laforestlabs/LLUPS/ROADMAP.md

# LLUPS Roadmap

> **Last updated:** 2026-05-04
> **Current phase:** Phase 7 -- parent composition quality tuning (board shrink + SMT-over-THT stacking)
> **Quick status:** Cluster-slide post-pass (KiCraft `072ceb6`) drops parent area 18-29% on seeds 4/7/42 by pulling drifting edge/corner-pinned components back into the cluster bbox after `solve()`. Best result: seed 7 at 11,058 mm² (was 15,400+). Follow-up `bbox_packing` sub-metric (KiCraft `a1456db`) adds an in-SA signal that drift costs PCB area, but at its current weight (0.01) it's below the SA temperature noise floor — plumbing is correct, layout impact is below detection threshold. KiCraft tests: 493 pass.

---

## How to use this file

This is the **single canonical plan document** for the LLUPS project. Every session should:
1. **Start** by reading this file to understand current state
2. **End** by updating the checkboxes, status line, and Last Session section below

This is the canonical plan; the CHANGELOG remains for detailed per-session engineering notes (append-only history).

---

## Phases Overview

| # | Phase | Status | Description |
|---|---|---|---|
| 0 | Repo cleanup and KiCraft extraction | Done | Untrack artifacts, consolidate docs, extract KiCraft submodule |
| 1 | KiCraft dead code removal (Wave 1-3) | Done | Delete dead code, fix imports, clean GUI |
| 2 | KiCraft code cleanup | Done | Delete dead CLIs, refactor subcircuit_instances, update docs |
| 3 | Leaf pipeline hardening | Done | Fix pre-route leaf legality, acceptance gates, anchor completeness |
| 4 | Parent composition MVP | Done | Compose parent from real routed leaves, parent FreeRouting |
| 5 | Recursive hierarchy | Done | Bottom-up N-level solve (algorithm verified on synthetic 4-level hierarchy; no real 3+ level schematic exists in this project) |
| 6 | Production polish | Done | Force tuning, FreeRouting crash reduction, test coverage |
| 7 | Parent composition quality | In progress | SMT-over-THT stacking, board shrink, rotation search per unconstrained leaf |

---

## Phase 0: Repo Cleanup and KiCraft Extraction (done)

All complete.

- [x] Untrack .experiments/ and generated artifacts from git
- [x] Consolidate .gitignore
- [x] Delete stale handoff files and backups
- [x] Consolidate 3 overlapping roadmap/next-steps docs
- [x] Add clean-experiments CLI
- [x] Decouple KiCraft from LLUPS hardcodes
- [x] Extract KiCraft to standalone repo with pyproject.toml
- [x] Reintegrate as git submodule (pip install -e KiCraft/)
- [x] GitHub Actions CI (ruff + pytest on 3.10/3.12/3.13)
- [x] Tag KiCraft v0.1.0

---

## Phase 1: KiCraft Dead Code Removal (done)

- [x] Wave 1: Delete ~3,000 lines of dead code (commit 3b47044)
- [x] Wave 2: Fix fragile imports, normalize scoring weights, consolidate plot CLIs (commit 60477fa)
- [x] Wave 3 / Phase 1 GUI cleanup: Delete param_sensitivity module, remove dead GUI toggles/flags, fix preloaded_path bug (commit c7e85ae)
- [x] Add minimal test gate rules to AGENTS.md

---

## Phase 2: KiCraft Code Cleanup (done)

- [x] Delete dead CLI modules: layout_session.py, dashboard_app.py
- [x] Remove dead entry points from pyproject.toml (layout-session, dashboard-app)
- [x] Clean score_layout.py: remove --no-track flag and broken session-tracking block
- [x] Refactor subcircuit_instances.py with normalize-early pattern (1 normalizer + 6 shared parsers, ~90 lines removed)
- [x] Update SKILL.md (both copies): remove deleted commands, fix plot-experiments to plot-results
- [x] Run verification: pytest 94 pass, import smoke OK, ruff clean
- [x] Commit and push KiCraft changes (7d02220)
- [x] Update LLUPS submodule pointer

---

## Phase 3: Leaf Pipeline Hardening (complete)

The leaf pipeline works end-to-end but stamped pre-route leaf boards are sometimes illegal geometry, causing FreeRouting to fail. This phase makes leaves reliably legal.

- [x] Fix root parent validation bug: was rejecting with missing_required_anchors despite successful routing (commit 939ff28)
- [x] Add leaf anchor completeness warning: _persist_solution now warns when required ports are unanchored
- [x] Fix pcbnew environment: venv had include-system-site-packages=false, blocking KiCad 9.0.8 bindings
- [x] Fix list_footprints.py: add argparse so --help works without crashing pcbnew
- [x] Verify full pipeline with pcbnew environment: all 6 leaves solve, route, and get accepted
- [x] Create brain/leaf_acceptance.py: configurable acceptance gate module (DRC, anchor, legality gates)
- [x] Add tests for subcircuit_extractor (14 tests)
- [x] Add tests for hierarchy levels / _compute_levels (6 tests)
- [x] Add tests for subcircuit_composer (7 tests)
- [x] Add tests for leaf_acceptance module (10 tests)
- [x] Integrate leaf_acceptance module into solve_subcircuits.py (replace inline acceptance logic)
- [x] Fix stamped pre-route leaf legality for edge-pinned connectors (USB INPUT leaf)
- [x] Fix LLUPS leaf anchor completeness (USB INPUT has only VBUS port; GND is implicit, needs explicit interface port)

---

## Phase 4: Parent Composition MVP (complete)

Key MVP milestone: a parent board composed from real routed leaves, inspectable in KiCad.

- [x] Compose root parent from accepted routed leaf artifacts (child copper stamped via DSN locking)
- [x] Run parent FreeRouting without clearing child copper
- [x] Human-inspectable output in KiCad before and after parent routing (renders generated)
- [x] Reproducible from CLI without manual patching (solve-hierarchy --skip-leaves --route)
- [x] Add copper accounting verification (fingerprint-based trace matching, per-child preservation reporting)

**MVP success:** Pipeline verified -- parent composed and routed with 6 leaves (leaf solving via solve-subcircuits, parent composition via solve-hierarchy --skip-leaves --route). Output is reproducible from CLI and human-inspectable in KiCad. The parent acceptance gate rejects due to FreeRouting routing quality (a tuning concern, not a functional gap -- the MVP goal was end-to-end composition and routing for human inspection, which is achieved).

---

## Phase 5: Recursive N-Level Hierarchy (complete)

- [x] Bottom-up level-by-level traversal via _compute_levels() (commit 939ff28)
- [x] Update solve-hierarchy CLI for full recursive N-level flow
- [x] Add test coverage for _compute_levels with 3+ level hierarchies (test_hierarchy_levels.py)
- [x] Synthetic 3+ level hierarchy verified in tests (TestThreeLevelHierarchy, TestDeepChain with 4 levels)
- [x] End-to-end solve-hierarchy --skip-leaves --route verified on LLUPS (2-level: root + 6 pre-solved leaves, 47.1s)

**Note:** LLUPS has only 2 levels (root + 6 leaves), so no real >2-level schematic exists in this project. The recursive algorithm was validated with synthetic 4-level tests.

---

## Phase 6: Production Polish (complete)

- [x] Improve test coverage: 287 tests total (100 added since Phase 3 baseline of 187: copper_accounting 22, leaf_passive_ordering 30, leaf_geometry 4, plus the 44 in dedicated checkboxes below)
- [x] Tune force balance for better component spread (SA refinement + config parameter mutation)
- [x] Reduce FreeRouting crash rate (~6% to <1%) (DSN trace locking for copper preservation)
- [x] Deduplicate force simulation code (_force_step vs _force_step_numpy in placement.py) + fix missing center-attraction bug
- [x] Extract algorithmic code from solve_subcircuits.py into brain/leaf_geometry.py (8 functions moved)
- [x] Split brain/placement.py into focused modules (placement_solver.py, placement_scorer.py, placement_utils.py)
- [x] Extract passive ordering code into brain/leaf_passive_ordering.py (6 functions, ~360 lines)
- [x] Add simulated annealing refinement to PlacementSolver (displacement, swap, rotation moves with Metropolis acceptance)
- [x] Add CONFIG_SEARCH_SPACE and _mutate_config to autoexperiment (Gaussian perturbation of 18 parameters)
- [x] Replace binary scoring cliffs with continuous functions (placement_check, types.py, geometry_check)
- [x] Add DSN trace locking for copper preservation during parent routing (freerouting_runner.py)
- [x] Fix implicit interface port role: POWER -> POWER_IN (subcircuit_extractor.py)
- [x] Add tests for _mutate_config and CONFIG_SEARCH_SPACE (26 tests in test_mutate_config.py)
- [x] Add tests for _sa_refine (8 tests in test_sa_refine.py)
- [x] Add tests for _infer_implicit_interface_ports (10 tests in test_implicit_interface_ports.py)
- [x] Extract _attempt_leaf_size_reduction into brain/leaf_size_reduction.py (~500 lines)
- [x] Extract _route_local_subcircuit into brain/leaf_routing.py (~750 lines)
- [x] Move SolveRoundResult dataclass to brain/types.py (clean dependency)
- [x] Reduce solve_subcircuits.py from 2579 to 1315 lines (49% reduction)
- [x] Verify copper preservation at parent level: 95.6% traces (237/248), 80% vias (4/5) via solve-hierarchy --skip-leaves --route. Per-child: BOOST 100%, LDO 100%, CHARGER 94%, USB INPUT 97.2%, BATT PROT 84.6%, BT1 100%. Trace target >95% met overall; individual children vary per FreeRouting routing decisions.
- [x] Full pipeline verification via solve-hierarchy --skip-leaves --route: parent composed from 6 pre-solved leaves and routed in 47.1s
- [x] Verify implicit ports end-to-end: USB INPUT leaf (uses implicit GND port) was solved+routed+accepted by solve-subcircuits, then composed into parent by solve-hierarchy. Both stages run to completion without Python exceptions.

---

## Architecture Reference

### Pipeline flow

  solve-subcircuits (per-leaf solve + FreeRouting)
    -> .experiments/subcircuits/<slug>/solved_layout.json
  compose-subcircuits (assemble leaves into parent, stamp + FreeRoute parent)
    -> .experiments/subcircuits/<parent>/...
  solve-hierarchy (orchestrates full bottom-up recursive solve)
    -> calls solve-subcircuits + compose-subcircuits per level
  autoexperiment (multi-round outer loop)
    -> calls solve-subcircuits + compose-subcircuits as subprocesses

### Key facts

- FreeRouting is the sole routing engine for both leaf and parent levels.
- KiCraft is a git submodule at KiCraft/. Install with pip install -e KiCraft/.
- Project config: LLUPS_autoplacer.json
- Artifacts: .experiments/ (gitignored, regenerable)
- pcbnew: system-installed at /usr/lib64/python3.13/site-packages/ (KiCad 9.0.8)
- venv must have include-system-site-packages=true for pcbnew access

### Key files

| File | Role |
|---|---|
| KiCraft/kicraft/cli/solve_subcircuits.py | Leaf solve + FreeRouting orchestration (1315 lines, thin wrappers) |
| KiCraft/kicraft/cli/compose_subcircuits.py | Parent composition + stamp + FreeRoute |
| KiCraft/kicraft/cli/solve_hierarchy.py | Top-level recursive orchestrator |
| KiCraft/kicraft/autoplacer/brain/subcircuit_solver.py | Interface anchor inference + leaf silkscreen helpers |
| KiCraft/kicraft/autoplacer/brain/subcircuit_composer.py | Parent composition logic |
| KiCraft/kicraft/autoplacer/brain/subcircuit_instances.py | Artifact loading + transform |
| KiCraft/kicraft/autoplacer/brain/subcircuit_extractor.py | Leaf extraction from full board |
| KiCraft/kicraft/autoplacer/brain/leaf_acceptance.py | Configurable leaf acceptance gates |
| KiCraft/kicraft/autoplacer/brain/leaf_routing.py | FreeRouting leaf routing orchestration (~750 lines) |
| KiCraft/kicraft/autoplacer/brain/leaf_size_reduction.py | Leaf size reduction + local solver config (~500 lines) |
| KiCraft/kicraft/autoplacer/brain/hierarchy_parser.py | Schematic hierarchy parsing |
| KiCraft/kicraft/autoplacer/brain/placement_solver.py | Force-directed placement solver |
| KiCraft/kicraft/autoplacer/brain/placement_scorer.py | Placement quality scorer |
| KiCraft/kicraft/autoplacer/brain/placement_utils.py | Shared placement geometry helpers |
| KiCraft/kicraft/autoplacer/brain/leaf_passive_ordering.py | Passive topology analysis and ordering |
| KiCraft/kicraft/autoplacer/hardware/adapter.py | KiCad pcbnew API interface |
| KiCraft/kicraft/autoplacer/freerouting_runner.py | FreeRouting Java process wrapper |

---

## Last Session Handoff

**Date:** 2026-05-04

### Completed since last handoff (sessions spanning 2026-05-02 → 2026-05-04)

1. Wired `--seed` through `compose_subcircuits` so random search varies parent layouts per round (KiCraft `d4ec6ad`).
2. Rebalanced parent-composition weights: `area_utilization` 0.15→0.25, `packing_density` 0.25→0.15 (KiCraft `e438586`).
3. Tightened LLUPS-level DRC defaults to OSH Park 2-layer service spec: `min_clearance` 0.2→0.1524 mm, `min_copper_edge_clearance` 0.0→0.381 mm (LLUPS `9fc6488`).
4. Cluster-slide post-pass: pulls drifting edge/corner-pinned components back into the cluster bbox after `solve()` (KiCraft `072ceb6`). Parent area drops 18-29% on seeds 4/7/42; best 11,058 mm² on seed 7.
5. Shared `packing_metrics` helper extracted to `placement_utils.py` so `_score_parent_composition` and the new `_score_bbox_packing` cannot drift in their definition of "tightly packed" (KiCraft `7491fdd`).
6. New `bbox_packing` sub-metric on `PlacementScorer` at weight 0.01 absorbed from `compactness` (KiCraft `a1456db`). Plumbing is correct; weight is below SA temperature noise floor and layouts stay bit-identical to the slide-only baseline. C3 attempt at weight 0.05 (sourced from `crossover_score`) also bit-identical, reverted before commit.
7. Tests: 488 → 493. New `tests/test_placement_scorer_bbox_packing.py` covers tight (>=90), spread (<50), single, empty, and zero-area NaN-defence.

### Open follow-ups (for next session)

- Find a working weight for `bbox_packing` (0.05 was insufficient; 0.10+ or a different intervention point may be needed).
- Per-unconstrained-leaf rotation search during packing (still open).
- Verify the cluster-slide pass does not regress edge-constrained placements under longer autoexperiment runs (visual check on seeds 4/7/42 is fine).
- Locally-modified GUI / CLI files popped from a 2026-05-03 stash on 2026-05-04 (within-run leaf round accumulation feature + KiCraft-side OSH Park sync) — review and commit when ready. Touches `kicraft/autoplacer/config.py`, `kicraft/cli/program.md`, `kicraft/cli/solve_subcircuits.py`, `kicraft/gui/components/{node_detail,pipeline_graph,per_component}.py`, `kicraft/gui/pages/monitor.py`, `tests/test_run_artifact_cleanup.py`.

---

## Phase 7: Parent Composition Quality (in progress)

The pipeline is end-to-end functional, but the composed parent board is
larger than it should be because unconstrained SMT leaves were not
stacking onto the front side above back-dominant THT leaves (the
battery holders).

- [x] Fix `_find_non_overlapping_origin` to pick the candidate with
      maximum overlap area instead of the first legal overlap encountered
      in the y-major raster. (KiCraft `feat/project-plan-layer` 831be3b)
- [x] Weight overlap scoring by opposite-side dominance so front-on-back
      stacking wins over same-side pad-gap stacking. (KiCraft `dbe021a`)
- [x] Wire `--seed` through `compose_subcircuits` -> `_compose_artifacts`
      so parent random search actually varies layouts per round.
      (KiCraft `d4ec6ad`)
- [x] Reweight parent composition score: `area_utilization` 0.15 -> 0.25,
      `packing_density` 0.25 -> 0.15, so the optimiser prefers smaller
      boards over densely-packed-but-large boards. (KiCraft `e438586`)
- [x] Slide edge/corner-pinned components back to the cluster bbox after
      `solve()`. (KiCraft `072ceb6`) Drops parent area 18-29% on seeds
      4/7/42 (best: seed 7 at 11,058 mm²).
- [x] Extract a shared `packing_metrics` helper and add a position-
      dependent `bbox_packing` sub-metric to `PlacementScorer` (the
      pre-existing `compactness` divided by the fixed seed frame, which
      contributed a constant during a solve). (KiCraft `7491fdd`,
      `a1456db`) At weight 0.01 the metric is below the SA temperature
      noise floor; layouts are bit-identical to the slide-only baseline.
- [ ] Find a working weight for `bbox_packing`. Tried 0.05 sourced from
      `crossover_score: 0.17 -> 0.13` -- still bit-identical. The
      dominant placement metrics drown out a 5-weighted-points attractor.
      Future options: weight 0.10+, a different SA temperature schedule,
      or wiring the metric into the force-directed phase.
- [ ] Per-unconstrained-leaf rotation search during packing. The current
      `_make_unconstrained_model` rotation is a static function of the
      leaf index; real rotation search would let a leaf pick the
      orientation that maximises overlap with already-placed leaves.
- [ ] Verify the slide pass does not regress edge-constrained placements
      under autoexperiment-scale runs (USB INPUT, LDO 3.3V). Visual check
      on seeds 4/7/42 shows both still on their assigned edges.

### Remaining (future improvements -- not required for functional MVP)

These items are either validation coverage gaps (no test asset exists) or output quality tuning targets. The pipeline is functional end-to-end; none of these block that claim.

1. Real multi-level schematic testing (LLUPS is 2-level; algorithm verified via synthetic 4-level tests)
2. Board size search parameter tuning (CONFIG_SEARCH_SPACE has it, needs extended autoexperiment runs)
3. Parent acceptance gate quality: currently rejected as illegal_routed_geometry -- FreeRouting routing quality needs parameter tuning to pass the gate
4. Via preservation: 80% (4/5) -- one via lost during parent routing, investigate FreeRouting DSN locking parameters

### Verification state
- pytest: 287 passed, 0 skipped (pass)
- Import smoke: All critical imports OK (pass)
- ruff: All checks passed
- solve-hierarchy --skip-leaves --route: completed in 47.1s, parent_routed.kicad_pcb + solved_layout.json written (--skip-leaves is intentional: reuses pre-solved+accepted leaf artifacts rather than redundantly re-solving them)
- solve-subcircuits --rounds 1 --route: all 6 leaves solved+routed+accepted (7 solved_layout.json on disk)
- Copper trace preservation: 95.6% (237/248) -- >95% target MET
- Copper via preservation: 80% (4/5) -- one via lost
- Implicit ports: USB INPUT leaf with implicit GND solved and composed successfully
- Parent acceptance: rejected (illegal_routed_geometry) -- quality tuning target, not a functional gap (pipeline runs to completion and produces inspectable output)
