laforestlabs/LLUPS/report.html

# PCB Layout Experiment Report

3

Total Rounds

1

Improvements

91.32

Best Score

44s

Total Time

0

Worst Shorts

0

Failing Nets

## ▸ Score Timeline

## ▸ PCB Layout Gallery

◀ Prev Next ▶ Auto-play

No frames available

No frame images found in .experiments/frames/

## ▸ Metrics Across Rounds

## ▸ Round Browser (3 rounds)

Kept only

Round | Score | Mode | Duration | Routed | Vias | Shorts | DRC | Status

## ▸ Net Failure Analysis (0 failing nets)

Net | Attempts | Failures | Reasons
No net failures

## ▸ Shorts Dashboard

Round | Score | Shorts | Nets | Locations
No shorts in any round

## ▸ Configuration Sensitivity
